usini/m1d1_36/docs/event_based.png

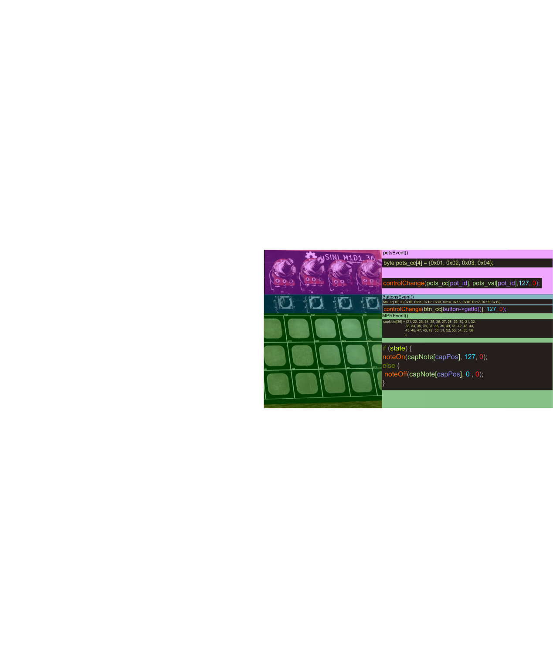
docs/event_based.png
