usini/m1d1_36/docs/images/m1d1_36_mpr121.jpg

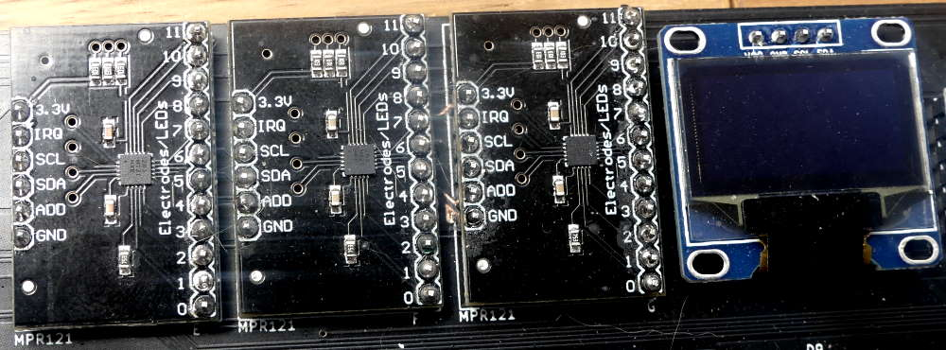
docs/images/m1d1_36_mpr121.jpg
