usini/m1d1_36/docs/images/m1d1_36_pots.jpg

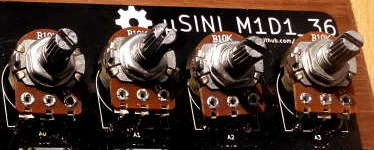
docs/images/m1d1_36_pots.jpg
