usini/m1d1_36/docs/images/mpr121.jpg

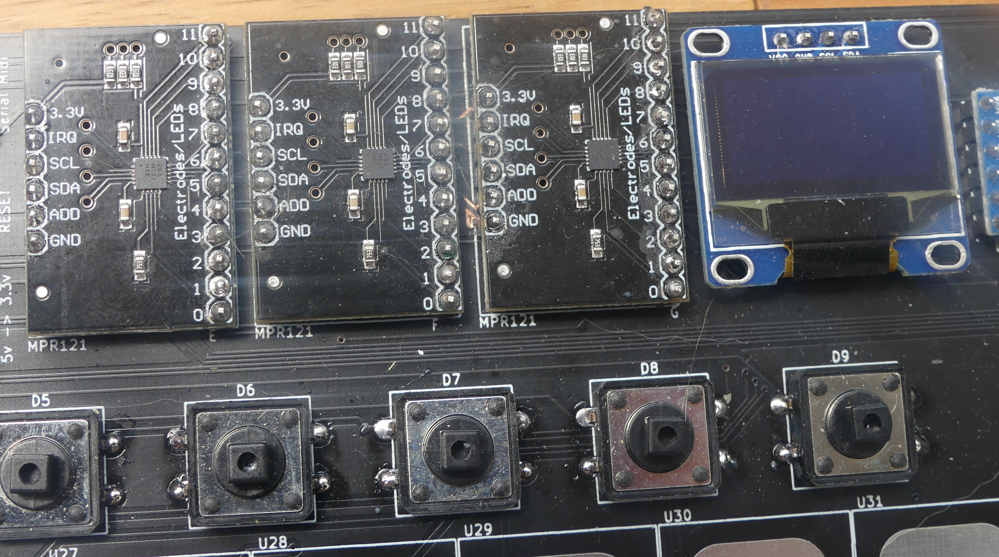
docs/images/mpr121.jpg
