usini/m1d1_36/kicad/m1d1_36/render/m1d1_36_texture.png

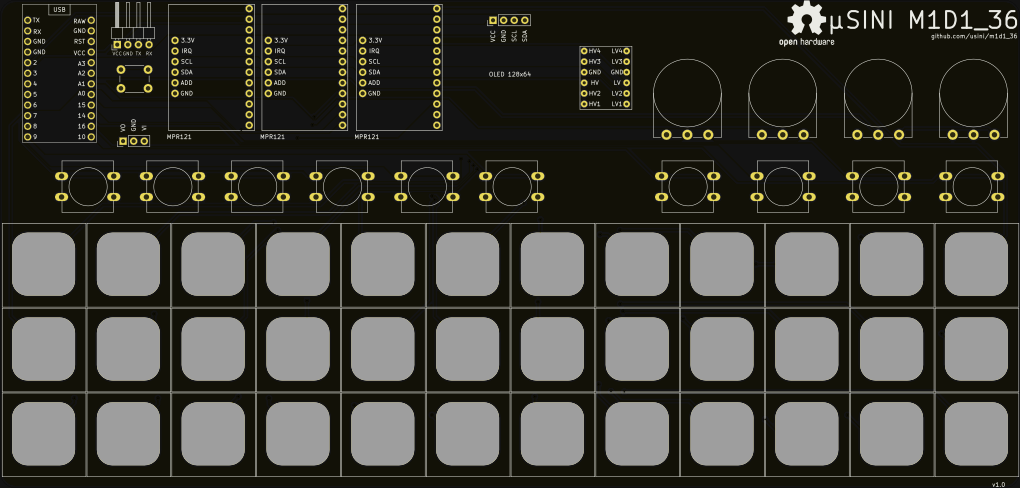
kicad/m1d1_36/render/m1d1_36_texture.png
